yasith46/METROBAND/Code/src/icons.h

// 'bton', 33x15px
const unsigned char ch_bton [] PROGMEM = {
	0x03, 0xc0, 0x0e, 0x44, 0x00, 0x03, 0xe0, 0x11, 0x44, 0x00, 0x23, 0x70, 0x11, 0x64, 0x00, 0x33, 
	0x38, 0x11, 0x54, 0x00, 0x1b, 0x1c, 0x11, 0x4c, 0x00, 0x0f, 0x38, 0x11, 0x44, 0x00, 0x47, 0x71, 
	0x0e, 0x44, 0x00, 0xe3, 0xe3, 0x80, 0x00, 0x00, 0x47, 0xe1, 0x00, 0x00, 0x00, 0x0f, 0x70, 0x00, 
	0x00, 0x00, 0x1b, 0x38, 0x00, 0x00, 0x00, 0x33, 0x1c, 0x00, 0x00, 0x00, 0x23, 0x38, 0x00, 0x00, 
	0x00, 0x03, 0x70, 0x00, 0x00, 0x00, 0x03, 0xe0, 0x00, 0x00, 0x00
};
// 'btsc', 33x15px
const unsigned char ch_btsc [] PROGMEM = {
	0x03, 0xc0, 0x00, 0x00, 0x00, 0x03, 0xe0, 0x00, 0x00, 0x00, 0x23, 0x70, 0x00, 0x00, 0x00, 0x33, 
	0x38, 0x00, 0x00, 0x00, 0x1b, 0x1c, 0x80, 0x00, 0x00, 0x0f, 0x38, 0x40, 0x00, 0x00, 0x07, 0x71, 
	0x40, 0x00, 0x00, 0x03, 0xe5, 0x40, 0x00, 0x00, 0x07, 0xe5, 0x4e, 0x38, 0x00, 0x0f, 0x71, 0x51, 
	0x44, 0x00, 0x1b, 0x38, 0x50, 0x40, 0x00, 0x33, 0x1c, 0x8e, 0x40, 0x00, 0x23, 0x38, 0x01, 0x40, 
	0x00, 0x03, 0x70, 0x11, 0x44, 0x00, 0x03, 0xe0, 0x0e, 0x38, 0x00
};
// 'chg', 12x15px
const unsigned char ch_chg [] PROGMEM = {
	0x02, 0x00, 0x06, 0x00, 0x06, 0x00, 0x0e, 0x00, 0x1e, 0x00, 0x1c, 0x00, 0x3f, 0xc0, 0x7f, 0xc0, 
	0x7f, 0xc0, 0x07, 0x80, 0x07, 0x00, 0x06, 0x00, 0x06, 0x00, 0x04, 0x00, 0x04, 0x00
};
// 'b100', 30x15px
const unsigned char ch_b100 [] PROGMEM = {
	0x07, 0xff, 0xff, 0xfc, 0x07, 0xff, 0xff, 0xfc, 0x06, 0x00, 0x00, 0x0c, 0x7e, 0xf7, 0xbd, 0xec, 
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
};


// Array of all bitmaps for convenience. (Total bytes used to store images in PROGMEM = 240)
const int challArray_LEN = 9;
const unsigned char* challArray[9] = {
	ch_b100,
	ch_b25,
	ch_b50,
	ch_b75,
	ch_bton,
	ch_btsc,
	ch_chg,
  ch_pl,
	ch_ps
};
